wwakabobik/home/home_server/pages/shared/tools.py

import math
from os import getcwd
from time import sleep, time

from plotly import graph_objects, offline
from picamera import PiCamera

from db.queries import data_update_period, get_last_series_measurement


camera = PiCamera()

units = {'temperature': '°C', 'humidity': '%', 'pressure': 'mm Hg', 'dew_point': '°C',
         'avg_voltage': 'V', 'avg_current': 'A', 'avg_power': 'W', 'avg_consumption': 'W/h',
         'avg_rps': 'rps', 'max_rps': 'rps', 'min_rps': 'rps',
         'avg_ms' : 'm/s', 'max_ms': 'm/s', 'min_ms': 'm/s',
         'avg_kmh': 'km/h', 'max_kmh': 'km/h', 'min_kmh': 'km/h',
         'avg_knots': 'knots', 'max_knots': 'knots', 'min_knots': 'knots',
         'heading': '°', 'precip': 'mm', 'uv': 'mW/cm^2'
         }


def convert_period(period):
    if period == "hour":
        num_period = int(60)
    elif period == "day":
        num_period = int(60 * 24)
    elif period == "week":
        num_period = int(60 * 24 * 7)
    elif period == "month":
        num_period = int(60 * 24 * 30)
    elif period == "year":
        num_period = int(60 * 24 * 365)
    else:
        raise Exception('Wrong period', f'{period}')
    return num_period


def convert_param(param, table):
    if table == 'weather_data':
        if "_in" in param:
            meas_type = 0
            fparam = param[:-3]
        elif "_out" in param:
            meas_type = 1
            fparam = param[:-4]
        else:
            meas_type = 0
            fparam = param
    else:
        fparam = param
        meas_type = None
    return fparam, meas_type


def generate_scatter(table, param, period, height=None, width=None):
    fparam, meas_type = convert_param(param, table)
    num_period = convert_period(period)
    x, y = get_last_series_measurement(table=table, period=num_period, param=fparam, meas_type=meas_type)
    line_chart1 = graph_objects.Scatter(x=x, y=y)
    lay1 = graph_objects.Layout(
        title=f'{param}',
        yaxis=dict(title=f'{units[fparam]}', ticks=f'inside'),
        height=height,
        width=width
    )
    fig1 = graph_objects.Figure(data=line_chart1, layout=lay1)
    offline_fig = offline.plot(fig1,
                               config={"displayModeBar": False},
                               show_link=False,
                               include_plotlyjs=True,
                               output_type='div')
    return offline_fig


def celsius_to_fahrenheit(celsius):
    farenheit = 9.0 / 5.0 * float(celsius) + 32
    return farenheit


def fahrenheit_to_celsius(farenheit):
    celsius = round(((farenheit - 32) * 5/9), 2)
    return celsius


def mmhg_to_baromin(mmhg):
    return float(mmhg)/25.4


def baromin_to_mmhg(baromin):
    return float(baromin*25.4)


def deg_to_heading(degrees=0):
    dirs = ['N', 'NE', 'E', 'SE', 'S', 'SW', 'W', 'NW']
    ix = round(degrees / (360. / len(dirs)))
    return dirs[ix % len(dirs)]


def heat_index(temp, hum):
    fahrenheit = celsius_to_fahrenheit(temp)
    # Creating multiples of 'fahrenheit' & 'hum' values for the coefficients
    t2 = pow(fahrenheit, 2)
    t3 = pow(fahrenheit, 3)
    h2 = pow(hum, 2)
    h3 = pow(hum, 3)

    # Coefficients for the calculations
    c1 = [-42.379, 2.04901523, 10.14333127, -0.22475541, -6.83783e-03, -5.481717e-02, 1.22874e-03, 8.5282e-04,
          -1.99e-06]
    c2 = [0.363445176, 0.988622465, 4.777114035, -0.114037667, -0.000850208, -0.020716198, 0.000687678, 0.000274954, 0]
    c3 = [16.923, 0.185212, 5.37941, -0.100254, 0.00941695, 0.00728898, 0.000345372, -0.000814971, 0.0000102102,
          -0.000038646, 0.0000291583, 0.00000142721, 0.000000197483, -0.0000000218429, 0.000000000843296,
          -0.0000000000481975]

    # Calculating heat-indexes with 3 different formula
    heatindex1 = c1[0] + (c1[1] * fahrenheit) + (c1[2] * hum) + (c1[3] * fahrenheit * hum) + (c1[4] * t2) + (
                c1[5] * h2) + (c1[6] * t2 * hum) + (c1[7] * fahrenheit * h2) + (c1[8] * t2 * h2)
    heatindex2 = c2[0] + (c2[1] * fahrenheit) + (c2[2] * hum) + (c2[3] * fahrenheit * hum) + (c2[4] * t2) + (
                c2[5] * h2) + (c2[6] * t2 * hum) + (c2[7] * fahrenheit * h2) + (c2[8] * t2 * h2)
    heatindex3 = c3[0] + (c3[1] * fahrenheit) + (c3[2] * hum) + (c3[3] * fahrenheit * hum) + (c3[4] * t2) + (
                c3[5] * h2) + (c3[6] * t2 * hum) + (c3[7] * fahrenheit * h2) + (c3[8] * t2 * h2) + (c3[9] * t3) + (
                             c3[10] * h3) + (c3[11] * t3 * hum) + (c3[12] * fahrenheit * h3) + (c3[13] * t3 * h2) + (
                             c3[14] * t2 * h3) + (c3[15] * t3 * h3)

    avg_heat_index = (heatindex1 + heatindex2 + heatindex3)/3.0
    return avg_heat_index


def humidex(t, d):
    kelvin = 273.15
    temperature = t + kelvin
    dewpoint = d + kelvin

    # Calculate vapor pressure in mbar.
    e = 6.11 * math.exp(5417.7530 * ((1 / kelvin) - (1 / dewpoint)))

    # Calculate saturation vapor pressure
    h = 0.5555 * (e - 10.0)

    hum_idex = temperature + h - kelvin

    return hum_idex


def take_photo():
    camera.resolution = (1280, 720)  # lower resolution to fit in 1mb limitation
    camera.start_preview()
    sleep(5)
    image = f'{getcwd()}/camera/image_{int(time())}.jpg'
    camera.capture(image)
    camera.stop_preview()
    return image
